AN63L/environment_monitoring_network/ESP32 BME680 and PMS7003/env-extra.py

from os.path import isfile

Import("env")
assert isfile(".env")
try:
    f = open(".env", "r")
    lines = f.readlines()
    envs = []
    for line in lines:
        envs.append("-D{}".format(line.strip()))
    env.Append(BUILD_FLAGS=envs)
    print("env: ", envs)
except IOError:
    print(
        "File .env not accessible",
    )
finally:
    f.close()
